SamuelMatamoros/Automating-the-care-of-a-plant/Documentos/Presentación/Recursos/Fotos/Crassula_Ovata_16cm-removebg-preview.png

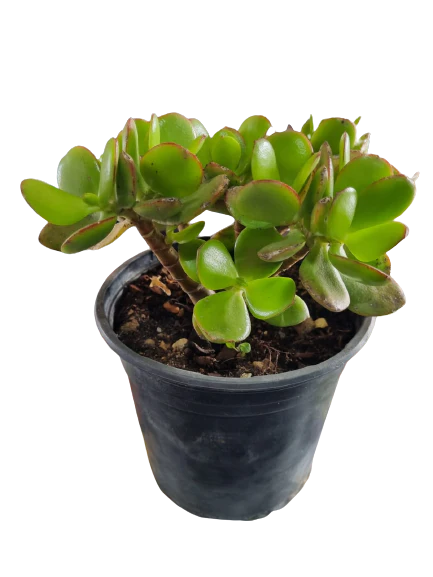
Documentos/Presentación/Recursos/Fotos/Crassula_Ovata_16cm-removebg-preview.png
