SamuelMatamoros/Automating-the-care-of-a-plant/Documentos/Presentación/Recursos/Fotos/front-view-fit-man-showing-bicep-with-copy-space-removebg-preview.png

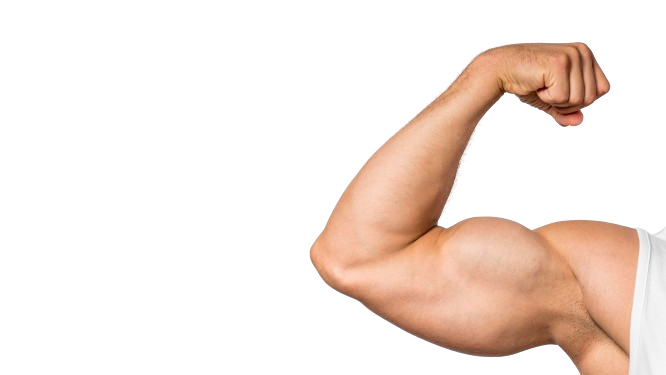
Documentos/Presentación/Recursos/Fotos/front-view-fit-man-showing-bicep-with-copy-space-removebg-preview.png
