SamuelMatamoros/Automating-the-care-of-a-plant/Documentos/Presentación/Recursos/Fotos/istockphoto-1214484654-612x612-removebg-preview.png

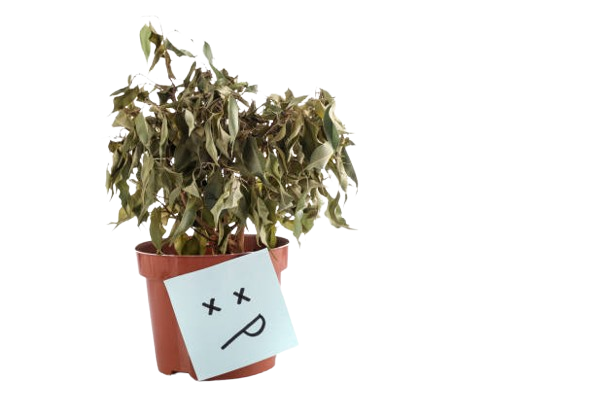
Documentos/Presentación/Recursos/Fotos/istockphoto-1214484654-612x612-removebg-preview.png
