SamuelMatamoros/Automating-the-care-of-a-plant/Documentos/Presentación/Recursos/Organigrama-black.png

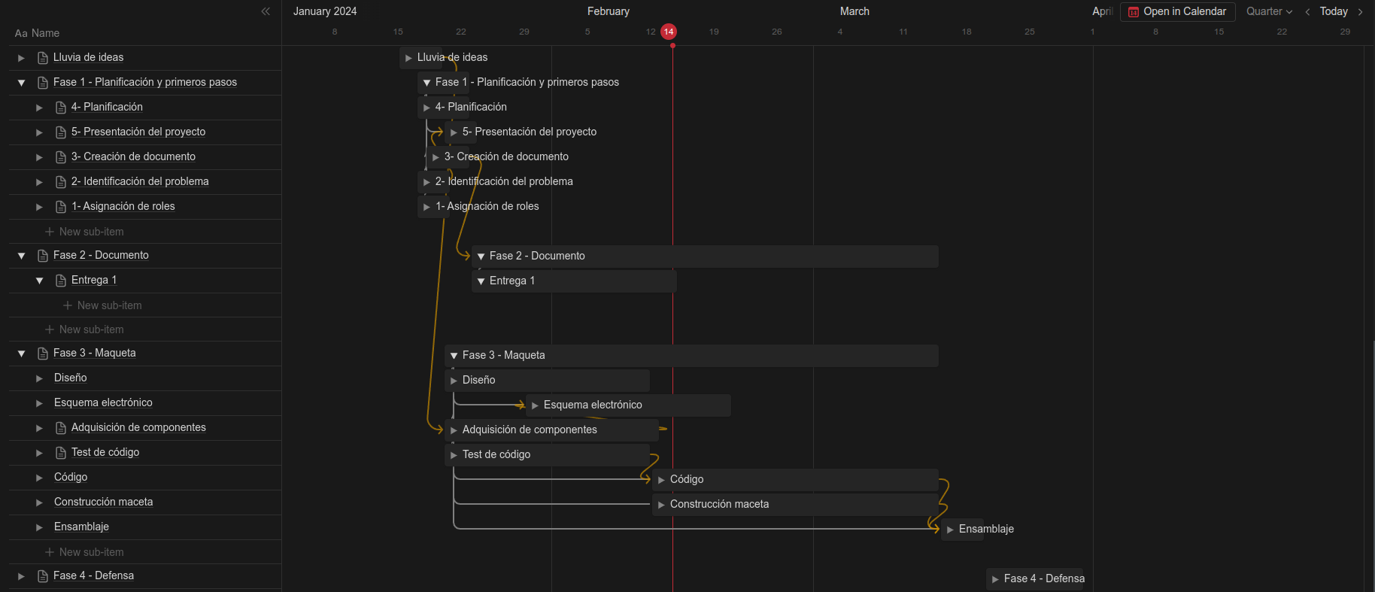
Documentos/Presentación/Recursos/Organigrama-black.png
