SamuelMatamoros/Automating-the-care-of-a-plant/Documentos/Presentación/RecursosDefensa/bg3.jpg

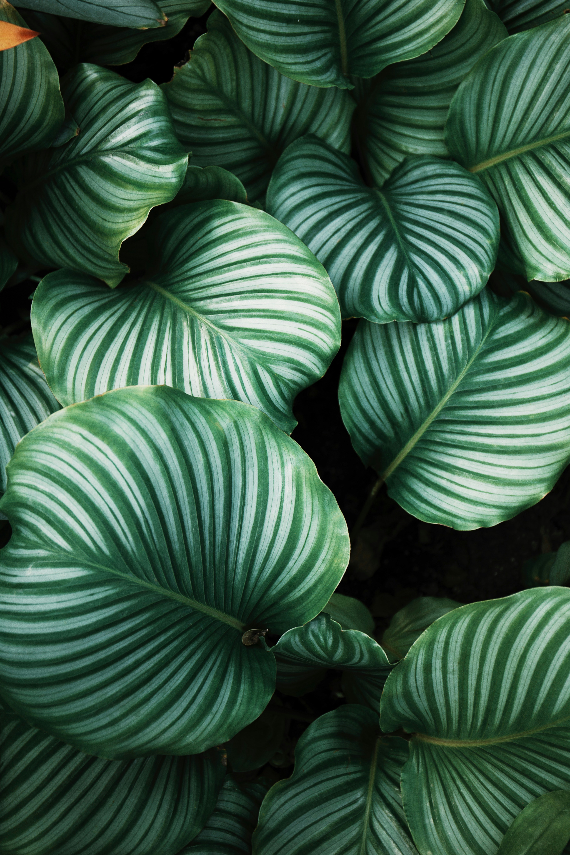
Documentos/Presentación/RecursosDefensa/bg3.jpg
