SamuelMatamoros/Automating-the-care-of-a-plant/Documentos/Presentación/RecursosDefensa/IMG20240409210344.jpg

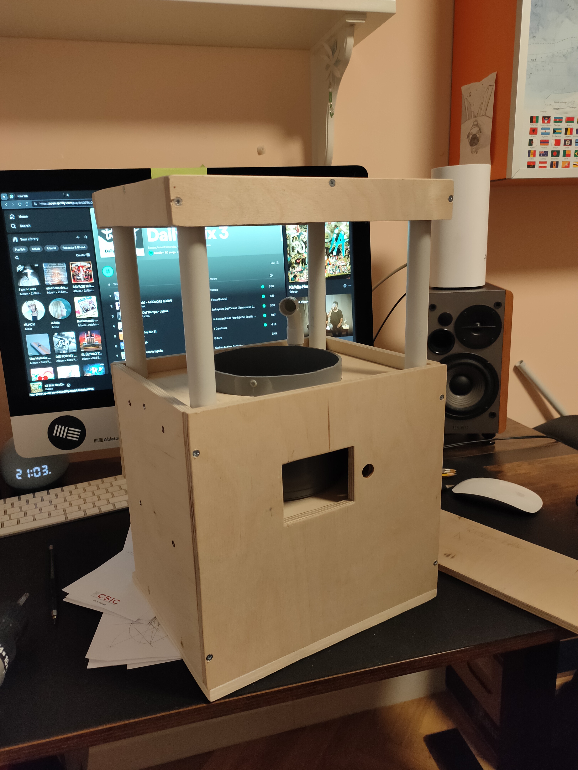
Documentos/Presentación/RecursosDefensa/IMG20240409210344.jpg
