SamuelMatamoros/Automating-the-care-of-a-plant/Documentos/Presentación/RecursosDefensa/IMG20240414233904.jpg

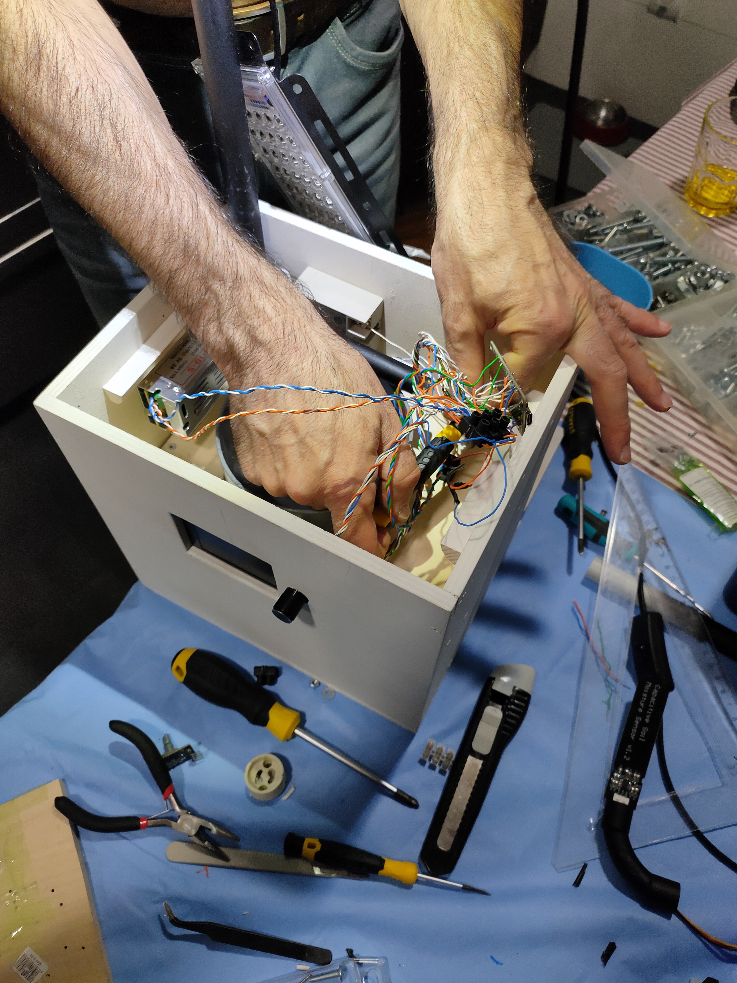
Documentos/Presentación/RecursosDefensa/IMG20240414233904.jpg
