SamuelMatamoros/Automating-the-care-of-a-plant/Documentos/Presentación/RecursosDefensa/IMG20240414233905.jpg

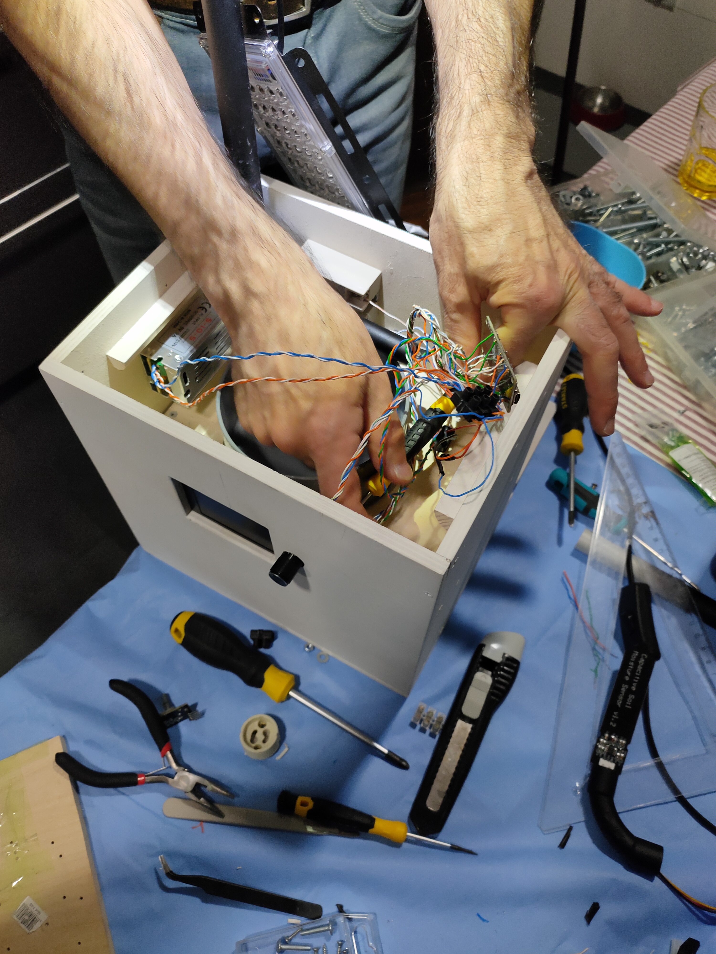
Documentos/Presentación/RecursosDefensa/IMG20240414233905.jpg
