SamuelMatamoros/Automating-the-care-of-a-plant/Documentos/Presentación/RecursosDefensa/IMG20240414233906.jpg

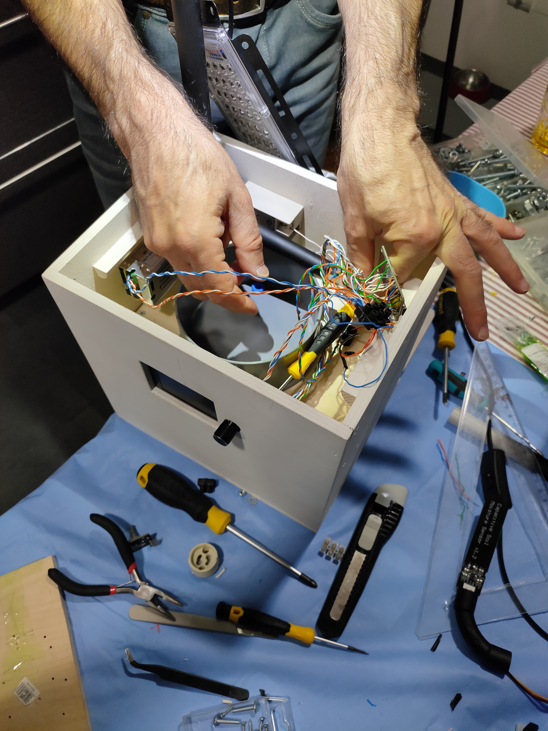
Documentos/Presentación/RecursosDefensa/IMG20240414233906.jpg
