SamuelMatamoros/Automating-the-care-of-a-plant/Diseño/Shematics/Shematics.kicad_sch

## KiCad design Diseño/Shematics/Shematics.kicad_sch (2024-04-11, an earlier design)

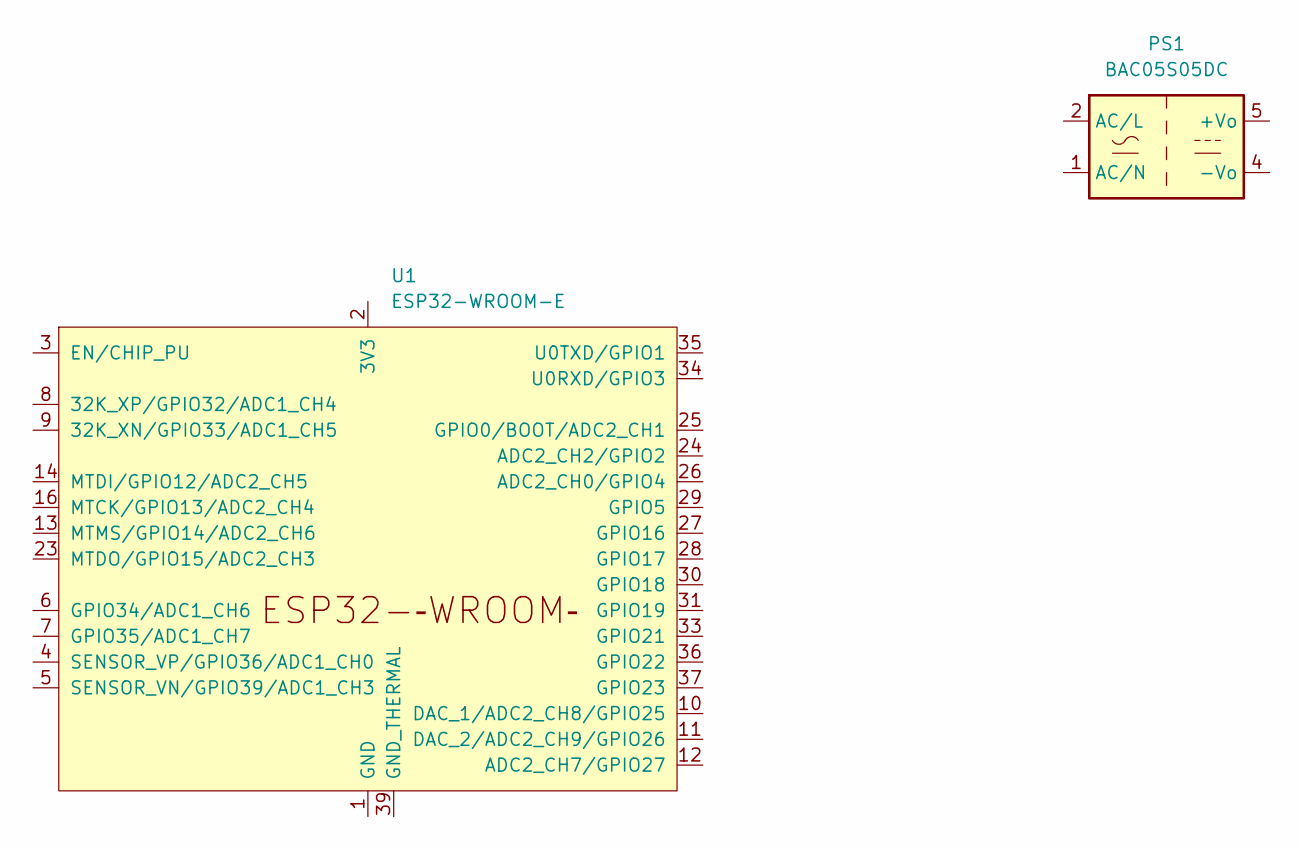
[picture p50: schematic Shematics.kicad_sch]

Parts:
PS1: BAC05S05DC; Converter_ACDC_Murata_BAC05SxxDC_THT
U1: ESP32-WROOM-E; ESP32-WROOM-32E

Connections:
unnamed: U1.1 (GND), U1.15 (GND), U1.38 (GND)
