SamuelMatamoros/Automating-the-care-of-a-plant/Código/esp32/src/main-DHT22.cpp

#include <Arduino.h>
#include <Adafruit_Sensor.h>
#include <DHT.h>
#include <DHT_U.h>

#define DHTPIN 32
#define DHTTYPE DHT22

DHT_Unified dht(DHTPIN, DHTTYPE);

uint32_t delayMS;

void setup() {

    Serial.begin(9600);

    dht.begin();
    Serial.println(F("DHT22 test"));

    sensor_t sensor;
    dht.temperature().getSensor(&sensor);
    Serial.println(F("------------------------------------"));
    Serial.println(F("Temperature Sensor"));
    Serial.print  (F("Sensor Type: ")); Serial.println(sensor.name);
    Serial.print  (F("Driver Ver:  ")); Serial.println(sensor.version);
    Serial.print  (F("Unique ID:   ")); Serial.println(sensor.sensor_id);
    Serial.print  (F("Max Value:   ")); Serial.print(sensor.max_value); Serial.println(F("°C"));
    Serial.print  (F("Min Value:   ")); Serial.print(sensor.min_value); Serial.println(F("°C"));
    Serial.print  (F("Resolution:  ")); Serial.print(sensor.resolution); Serial.println(F("°C"));
    Serial.println(F("------------------------------------"));

    dht.humidity().getSensor(&sensor);
    Serial.println(F("Humidity Sensor"));
    Serial.print  (F("Sensor Type: ")); Serial.println(sensor.name);
    Serial.print  (F("Driver Ver:  ")); Serial.println(sensor.version);
    Serial.print  (F("Unique ID:   ")); Serial.println(sensor.sensor_id);
    Serial.print  (F("Max Value:   ")); Serial.print(sensor.max_value); Serial.println(F("%"));
    Serial.print  (F("Min Value:   ")); Serial.print(sensor.min_value); Serial.println(F("%"));
    Serial.print  (F("Resolution:  ")); Serial.print(sensor.resolution); Serial.println(F("%"));
    Serial.println(F("------------------------------------"));

    delayMS = 2000;
}

void loop() {

    delay(delayMS);

    sensors_event_t event;
    dht.temperature().getEvent(&event);
    if (isnan(event.temperature)) {
    Serial.println(F("Error reading temperature!"));
    }
    else {
    Serial.print(F("Temperature: "));
    Serial.print(event.temperature);
    Serial.println(F("°C"));
    }

    dht.humidity().getEvent(&event);
    if (isnan(event.relative_humidity)) {
    Serial.println(F("Error reading humidity!"));
    }
    else {
    Serial.print(F("Humidity: "));
    Serial.print(event.relative_humidity);
    Serial.println(F("%"));
    }
}
